thetianshuhuang/rock-band/source/graphics/sd_data/back.bmp

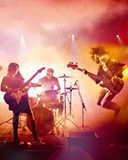
source/graphics/sd_data/back.bmp
