thetianshuhuang/rock-band/source/graphics/sd_data/menu_d.bmp

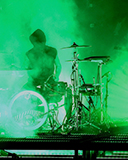
source/graphics/sd_data/menu_d.bmp
