thetianshuhuang/rock-band/source/graphics/sd_data/menu_g.bmp

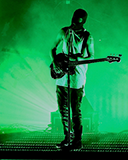
source/graphics/sd_data/menu_g.bmp
