thetianshuhuang/rock-band/source/accel/I2C0.c

// I2C0.c
// Runs on LM4F120/TM4C123
// Provide a function that initializes, sends, and receives the I2C0 module
// interfaced with an HMC6352 compass or TMP102 thermometer.
// Daniel Valvano
// July 2, 2014

/* This example accompanies the book
   "Embedded Systems: Real Time Interfacing to Arm Cortex M Microcontrollers",
   ISBN: 978-1463590154, Jonathan Valvano, copyright (c) 2013
   Section 8.6.4 Programs 8.5, 8.6 and 8.7

 Copyright 2013 by Jonathan W. Valvano, valvano@mail.utexas.edu
    You may use, edit, run or distribute this file
    as long as the above copyright notice remains
 THIS SOFTWARE IS PROVIDED "AS IS".  NO WARRANTIES, WHETHER EXPRESS, IMPLIED
 OR STATUTORY, INCLUDING, BUT NOT LIMITED TO, IMPLIED WARRANTIES OF
 MERCHANTABILITY AND FITNESS FOR A PARTICULAR PURPOSE APPLY TO THIS SOFTWARE.
 VALVANO SHALL NOT, IN ANY CIRCUMSTANCES, BE LIABLE FOR SPECIAL, INCIDENTAL,
 OR CONSEQUENTIAL DAMAGES, FOR ANY REASON WHATSOEVER.
 For more information about my classes, my research, and my books, see
 http://users.ece.utexas.edu/~valvano/
 */

// I2C0SCL connected to PE4
// I2C0SDA connected to PE5
// SCL and SDA lines pulled to +3.3 V with 10 k resistors (part of breakout module)
// ADD0 pin of TMP102 thermometer connected to GND
#include <stdint.h>
#include "../tm4c123gh6pm.h"

#define I2C_MCS_ACK             0x00000008  // Data Acknowledge Enable
#define I2C_MCS_DATACK          0x00000008  // Acknowledge Data
#define I2C_MCS_ADRACK          0x00000004  // Acknowledge Address
#define I2C_MCS_STOP            0x00000004  // Generate STOP
#define I2C_MCS_START           0x00000002  // Generate START
#define I2C_MCS_ERROR           0x00000002  // Error
#define I2C_MCS_RUN             0x00000001  // I2C Master Enable
#define I2C_MCS_BUSY            0x00000001  // I2C Busy
#define I2C_MCR_MFE             0x00000010  // I2C Master Function Enable

#define MAXRETRIES              5           // number of receive attempts before giving up
void I2C_Init(void){
  SYSCTL_RCGCI2C_R |= 0x0001;           // activate I2C0
  SYSCTL_RCGCGPIO_R |= 0x0010;          // activate port E
  while((SYSCTL_PRGPIO_R&0x0010) == 0){};// ready?

  GPIO_PORTE_AFSEL_R |= 0x30;           // 3) enable alt funct on PE4,5
  GPIO_PORTE_ODR_R |= 0x20;             // 4) enable open drain on PE5 only
  GPIO_PORTE_DEN_R |= 0x30;             // 5) enable digital I/O on PB2,3
                                        // 6) configure PE4,5 as I2C
  GPIO_PORTE_PCTL_R = (GPIO_PORTE_PCTL_R&0xFF00FFFF)+0x00330000;
  GPIO_PORTE_AMSEL_R &= ~0x30;          // 7) disable analog functionality on PE4,5
  I2C0_MCR_R = I2C_MCR_MFE;      // 9) master function enable
  I2C0_MTPR_R = 24;              // 8) configure for 100 kbps clock
  // 20*(TPR+1)*20ns = 10us, with TPR=24
}

// receives one byte from specified slave
uint8_t I2C_Recv(int8_t slave){
  int retryCounter = 1;
  do{
    while(I2C0_MCS_R&I2C_MCS_BUSY){};// wait for I2C ready
    I2C0_MSA_R = (slave<<1)&0xFE;    // MSA[7:1] is slave address
    I2C0_MSA_R |= 0x01;              // MSA[0] is 1 for receive
    I2C0_MCS_R = (0
                        // & ~I2C_MCS_ACK     // negative data ack (last byte)
                         | I2C_MCS_STOP     // generate stop
                         | I2C_MCS_START    // generate start/restart
                         | I2C_MCS_RUN);    // master enable
    while(I2C0_MCS_R&I2C_MCS_BUSY){};// wait for transmission done
    retryCounter = retryCounter + 1;        // increment retry counter
  }                                         // repeat if error
  while(((I2C0_MCS_R&(I2C_MCS_ADRACK|I2C_MCS_ERROR)) != 0) && (retryCounter <= MAXRETRIES));
  return (I2C0_MDR_R&0xFF);          // usually returns 0xFF on error
}
// receives two bytes from specified slave
// Used to read the contents of the pointer register
uint16_t I2C_Recv2(int8_t slave){
  uint8_t data1,data2;
  int retryCounter = 1;
  do{
    while(I2C0_MCS_R&I2C_MCS_BUSY){};// wait for I2C ready
    I2C0_MSA_R = (slave<<1)&0xFE;    // MSA[7:1] is slave address
    I2C0_MSA_R |= 0x01;              // MSA[0] is 1 for receive
    I2C0_MCS_R = (0
                         | I2C_MCS_ACK      // positive data ack
                       //  & ~I2C_MCS_STOP    // no stop
                         | I2C_MCS_START    // generate start/restart
                         | I2C_MCS_RUN);    // master enable
    while(I2C0_MCS_R&I2C_MCS_BUSY){};// wait for transmission done
    data1 = (I2C0_MDR_R&0xFF);       // MSB data sent first
    I2C0_MCS_R = (0
                       //  & ~I2C_MCS_ACK     // negative data ack (last byte)
                         | I2C_MCS_STOP     // generate stop
                       //  & ~I2C_MCS_START   // no start/restart
                         | I2C_MCS_RUN);    // master enable
    while(I2C0_MCS_R&I2C_MCS_BUSY){};// wait for transmission done
    data2 = (I2C0_MDR_R&0xFF);       // LSB data sent last
    retryCounter = retryCounter + 1;        // increment retry counter
  }                                         // repeat if error
  while(((I2C0_MCS_R&(I2C_MCS_ADRACK|I2C_MCS_ERROR)) != 0) && (retryCounter <= MAXRETRIES));
  return (data1<<8)+data2;                  // usually returns 0xFFFF on error
}

// sends one byte to specified slave
// Used to change the pointer register
// Returns 0 if successful, nonzero if error
uint32_t I2C_Send1(int8_t slave, uint8_t data1){
  while(I2C0_MCS_R&I2C_MCS_BUSY){};// wait for I2C ready
  I2C0_MSA_R = (slave<<1)&0xFE;    // MSA[7:1] is slave address
  I2C0_MSA_R &= ~0x01;             // MSA[0] is 0 for send
  I2C0_MDR_R = data1&0xFF;         // prepare first byte
  I2C0_MCS_R = (0
                    //   & ~I2C_MCS_ACK     // no data ack (no data on send)
                       | I2C_MCS_STOP     // generate stop
                       | I2C_MCS_START    // generate start/restart
                       | I2C_MCS_RUN);    // master enable
  while(I2C0_MCS_R&I2C_MCS_BUSY){};// wait for transmission done
                                          // return error bits
  return (I2C0_MCS_R&(I2C_MCS_DATACK|I2C_MCS_ADRACK|I2C_MCS_ERROR));
}

// Returns 0 if successful, nonzero if error
uint32_t I2C_Send2(int8_t slave, uint8_t data1, uint8_t data2){
  while(I2C0_MCS_R&I2C_MCS_BUSY){};// wait for I2C ready
  I2C0_MSA_R = (slave<<1)&0xFE;    // MSA[7:1] is slave address
  I2C0_MSA_R &= ~0x01;             // MSA[0] is 0 for send
  I2C0_MDR_R = data1&0xFF;         // prepare first byte
  I2C0_MCS_R = (0
                     //  & ~I2C_MCS_ACK     // no data ack (no data on send)
                    //   & ~I2C_MCS_STOP    // no stop
                       | I2C_MCS_START    // generate start/restart
                       | I2C_MCS_RUN);    // master enable
  while(I2C0_MCS_R&I2C_MCS_BUSY){};// wait for transmission done
                                          // check error bits
  if((I2C0_MCS_R&(I2C_MCS_DATACK|I2C_MCS_ADRACK|I2C_MCS_ERROR)) != 0){
    I2C0_MCS_R = (0                // send stop if nonzero
                     //  & ~I2C_MCS_ACK     // no data ack (no data on send)
                       | I2C_MCS_STOP     // stop
                     //  & ~I2C_MCS_START   // no start/restart
                     //  & ~I2C_MCS_RUN    // master disable
                        );   
                                          // return error bits if nonzero
    return (I2C0_MCS_R&(I2C_MCS_DATACK|I2C_MCS_ADRACK|I2C_MCS_ERROR));
  }
  I2C0_MDR_R = data2&0xFF;         // prepare second byte
  I2C0_MCS_R = (0
                      // & ~I2C_MCS_ACK     // no data ack (no data on send)
                       | I2C_MCS_STOP     // generate stop
                      // & ~I2C_MCS_START   // no start/restart
                       | I2C_MCS_RUN);    // master enable
  while(I2C0_MCS_R&I2C_MCS_BUSY){};// wait for transmission done
                                          // return error bits
  return (I2C0_MCS_R&(I2C_MCS_DATACK|I2C_MCS_ADRACK|I2C_MCS_ERROR));
}

// Used to change the contents of the pointer register
// Returns 0 if successful, nonzero if error
uint32_t I2C_Send3(int8_t slave, uint8_t data1, uint8_t data2, uint8_t data3){
  while(I2C0_MCS_R&I2C_MCS_BUSY){};// wait for I2C ready
  I2C0_MSA_R = (slave<<1)&0xFE;    // MSA[7:1] is slave address
  I2C0_MSA_R &= ~0x01;             // MSA[0] is 0 for send
  I2C0_MDR_R = data1&0xFF;         // prepare first byte
  I2C0_MCS_R = (0
                     //  & ~I2C_MCS_ACK     // no data ack (no data on send)
                     //  & ~I2C_MCS_STOP    // no stop
                       | I2C_MCS_START    // generate start/restart
                       | I2C_MCS_RUN);    // master enable
  while(I2C0_MCS_R&I2C_MCS_BUSY){};// wait for transmission done
                                          // check error bits
  if((I2C0_MCS_R&(I2C_MCS_DATACK|I2C_MCS_ADRACK|I2C_MCS_ERROR)) != 0){
    I2C0_MCS_R = (0                // send stop if nonzero
                     //  & ~I2C_MCS_ACK     // no data ack (no data on send)
                       | I2C_MCS_STOP     // stop
                     //  & ~I2C_MCS_START   // no start/restart
                     //  & ~I2C_MCS_RUN   // master disable
                       );   
                                          // return error bits if nonzero
    return (I2C0_MCS_R&(I2C_MCS_DATACK|I2C_MCS_ADRACK|I2C_MCS_ERROR));
  }
  I2C0_MDR_R = data2&0xFF;         // prepare second byte
  I2C0_MCS_R = (0
                     //  & ~I2C_MCS_ACK     // no data ack (no data on send)
                     //  & ~I2C_MCS_STOP    // no stop
                     //  & ~I2C_MCS_START   // no start/restart
                       | I2C_MCS_RUN);    // master enable
  while(I2C0_MCS_R&I2C_MCS_BUSY){};// wait for transmission done
                                          // check error bits
  if((I2C0_MCS_R&(I2C_MCS_DATACK|I2C_MCS_ADRACK|I2C_MCS_ERROR)) != 0){
    I2C0_MCS_R = (0                // send stop if nonzero
                     //  & ~I2C_MCS_ACK     // no data ack (no data on send)
                       | I2C_MCS_STOP     // stop
                     //  & ~I2C_MCS_START   // no start/restart
                     //  & ~I2C_MCS_RUN   // master disable
                        );
                                          // return error bits if nonzero
    return (I2C0_MCS_R&(I2C_MCS_DATACK|I2C_MCS_ADRACK|I2C_MCS_ERROR));
  }
  I2C0_MDR_R = data3&0xFF;         // prepare third byte
  I2C0_MCS_R = (0
                    //   & ~I2C_MCS_ACK     // no data ack (no data on send)
                       | I2C_MCS_STOP     // generate stop
                    //   & ~I2C_MCS_START   // no start/restart
                       | I2C_MCS_RUN);    // master enable
  while(I2C0_MCS_R&I2C_MCS_BUSY){};// wait for transmission done
                                          // return error bits
  return (I2C0_MCS_R&(I2C_MCS_DATACK|I2C_MCS_ADRACK|I2C_MCS_ERROR));
}
