thetianshuhuang/rock-band/source/PLL.h

// PLL.h
// Runs on LM4F120/TM4C123
// A software function to change the bus frequency using the PLL.
// Daniel Valvano
// May 3, 2015

/* This example accompanies the book
   "Embedded Systems: Real Time Interfacing to Arm Cortex M Microcontrollers",
   ISBN: 978-1463590154, Jonathan Valvano, copyright (c) 2015
   Program 2.10, Figure 2.37

 Copyright 2015 by Jonathan W. Valvano, valvano@mail.utexas.edu
    You may use, edit, run or distribute this file
    as long as the above copyright notice remains
 THIS SOFTWARE IS PROVIDED "AS IS".  NO WARRANTIES, WHETHER EXPRESS, IMPLIED
 OR STATUTORY, INCLUDING, BUT NOT LIMITED TO, IMPLIED WARRANTIES OF
 MERCHANTABILITY AND FITNESS FOR A PARTICULAR PURPOSE APPLY TO THIS SOFTWARE.
 VALVANO SHALL NOT, IN ANY CIRCUMSTANCES, BE LIABLE FOR SPECIAL, INCIDENTAL,
 OR CONSEQUENTIAL DAMAGES, FOR ANY REASON WHATSOEVER.
 For more information about my classes, my research, and my books, see
 http://users.ece.utexas.edu/~valvano/
 */

// The #define statement SYSDIV2 initializes
// the PLL to the desired frequency.
// SYSDIV = 400/freq -1
// bus frequency is 400MMHz/(SYSDIV+1)

// configure the system to get its clock from the PLL
void PLL_Init(uint32_t freq);
void Delayms(uint32_t ms);
#define Bus80MHz     4
#define Bus80_000MHz 4
#define Bus66_667MHz 5
#define Bus50_000MHz 7
#define Bus50MHz     7
#define Bus44_444MHz 8
#define Bus40_000MHz 9
#define Bus40MHz     9
#define Bus36_364MHz 10
#define Bus33_333MHz 11
#define Bus30_769MHz 12
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
#define Bus3_419MHz 116
#define Bus3_390MHz 117
#define Bus3_361MHz 118
#define Bus3_333MHz 119
#define Bus3_306MHz 120
#define Bus3_279MHz 121
#define Bus3_252MHz 122
#define Bus3_226MHz 123
#define Bus3_200MHz 124
#define Bus3_175MHz 125
#define Bus3_150MHz 126
#define Bus3_125MHz 127
