thetianshuhuang/rock-band/source/game/songs.c

/*
 * songs.c
 *
 * Song datatype definitions
 */
 
#include "songs.h"


SONG songs[6] = {
    {"rylah.bw", "rylah_g.rb", "rylah_b.rb", "rylah_d.rb", 11043000},
    {"miab.bw", "miab_g.rb", "miab_b.rb", "miab_d.rb", 12536000},
    {"wwl.bw", "wwl_g.rb", "wwl_b.rb", "wwl_d.rb", 9475000},
    {"zzz.bw", "zzz_g.rb", "zzz_b.rb", "zzz_d.rb", 8312000},
    {"hwr.bw", "hwr_g.rb", "hwr_b.rb", "hwr_d.rb", 10182000},
    {"tf.bw", "tf_g.rb", "tf_b.rb", "tf_d.rb", 10546000},
};
